neoviki/flexible.tactile.sensing.module.dual.sensors/01.Documents/Surface.Mounting.Equipments.Used.Images/IMG20240809145221.jpg

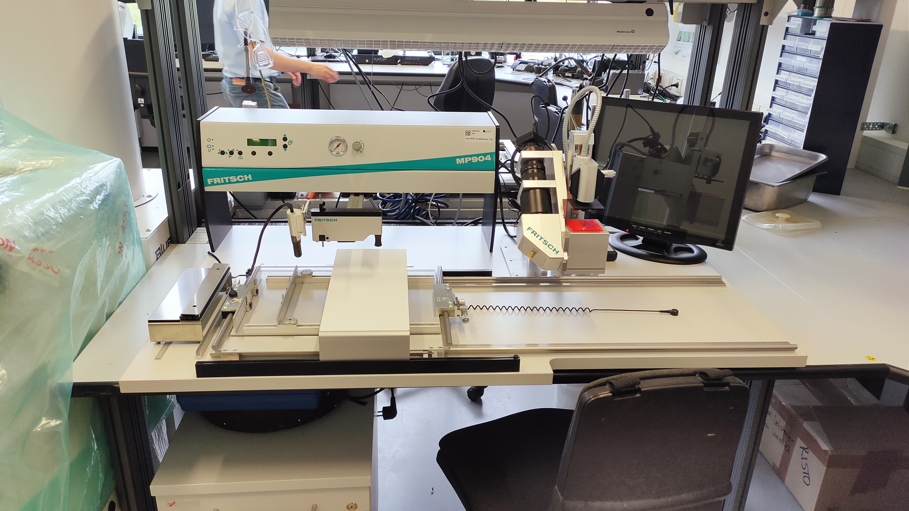
01.Documents/Surface.Mounting.Equipments.Used.Images/IMG20240809145221.jpg
