neoviki/flexible.tactile.sensing.module.dual.sensors/05.Images/sm.bottom.png

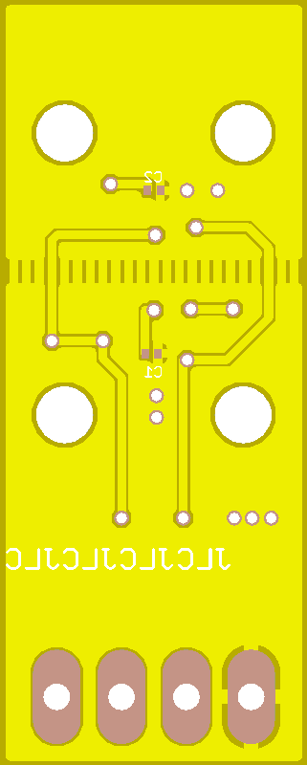
05.Images/sm.bottom.png
