neoviki/flexible.tactile.sensing.module.dual.sensors/05.Images/sm.top.png

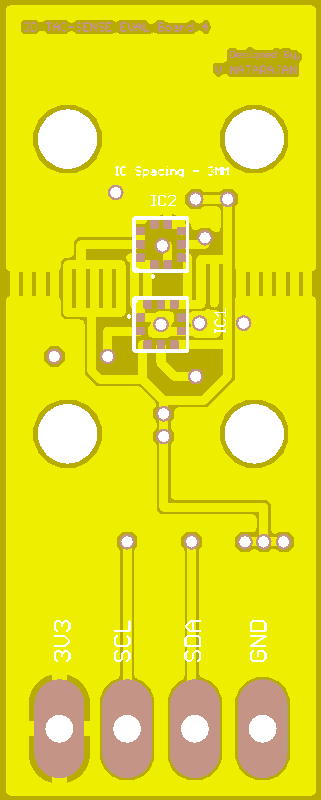
05.Images/sm.top.png
