neoviki/flexible.tactile.sensing.module.dual.sensors/01.Documents/Surface.Mounting.Equipments.Used.Images/low temperature solder paste 1.jpg

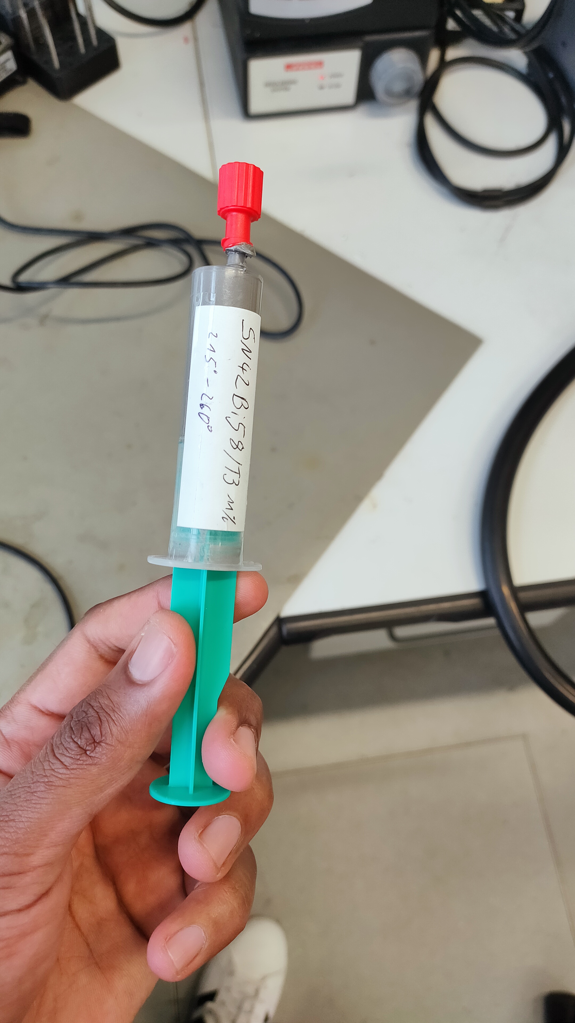
01.Documents/Surface.Mounting.Equipments.Used.Images/low temperature solder paste 1.jpg
