neoviki/flexible.tactile.sensing.module.dual.sensors/01.Documents/Surface.Mounting.Equipments.Used.Images/solder flux with high rosin content.jpg

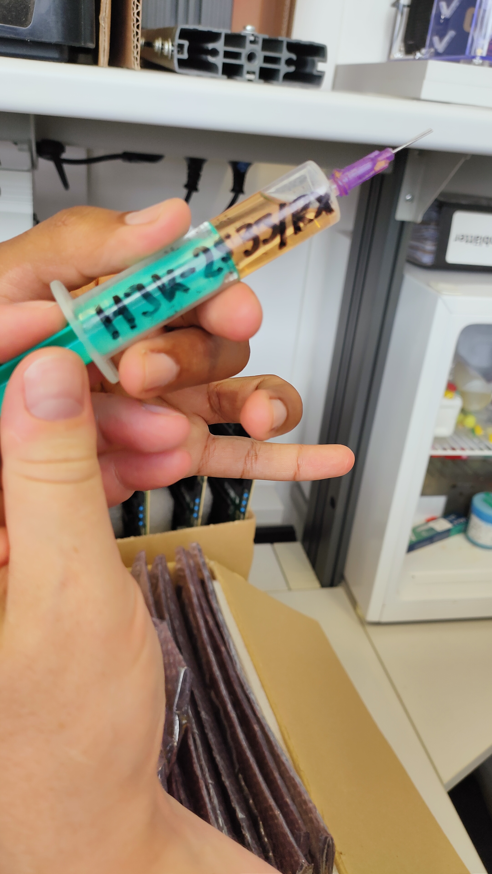
01.Documents/Surface.Mounting.Equipments.Used.Images/solder flux with high rosin content.jpg
